telec16/pong/ltspice/ball_speed.asc

C1: cap; 100n
C3: cap; 10µ
C4: cap; 470n
D1: diode; 1N4148
J1: njf; J111
Q1: npn; BC547B
Q2: npn; BC547B
Q3: pnp; BC557B
R1: res; 10k
R2: res; 10k
R3: res; 100k
R4: res; 330k
R5: res; 1k
R6: res; 100k
R7: res; 10k
R8: res; 10k
U1: opamp2; TL082
U2: opamp2; TL082
U3: opamp2; TL082
V1: voltage; 15
V2: voltage; 15
V3: voltage; PULSE(0 5 0 0 0 100m 5)
V4: voltage; PULSE(0 5 0 0 0 1000m 25)
V5: voltage; PULSE(5 0 0 0 0 1000m 25)
Named nets: 0, +15, -15, speed, reset, _speed, pos, inc, reset_speed
.tran 50 startup
* TL082 OPERATIONAL AMPLIFIER "MACROMODEL" SUBCIRCUIT
* CREATED USING PARTS RELEASE 4.01 ON 06/16/89 AT 13:08
* (REV N/A)      SUPPLY VOLTAGE: +/-15V
* CONNECTIONS:   NON-INVERTING INPUT
*                | INVERTING INPUT
*                | | POSITIVE POWER SUPPLY
*                | | | NEGATIVE POWER SUPPLY
*                | | | | OUTPUT
*                | | | | |
.SUBCKT TL082    1 2 3 4 5
*
  C1   11 12 3.498E-12
  C2    6  7 15.00E-12
  DC    5 53 DX
  DE   54  5 DX
  DLP  90 91 DX
  DLN  92 90 DX
  DP    4  3 DX
  EGND 99  0 POLY(2) (3,0) (4,0) 0 .5 .5
  FB    7 99 POLY(5) VB VC VE VLP VLN 0 4.715E6 -5E6 5E6 5E6 -5E6
  GA    6  0 11 12 282.8E-6
  GCM   0  6 10 99 8.942E-9
  ISS   3 10 DC 195.0E-6
  HLIM 90  0 VLIM 1K
  J1   11  2 10 JX
  J2   12  1 10 JX
  R2    6  9 100.0E3
  RD1   4 11 3.536E3
  RD2   4 12 3.536E3
  RO1   8  5 150
  RO2   7 99 150
  RP    3  4 2.143E3
  RSS  10 99 1.026E6
  VB    9  0 DC 0
  VC    3 53 DC 2.200
  VE   54  4 DC 2.200
  VLIM  7  8 DC 0
  VLP  91  0 DC 25
  VLN   0 92 DC 25
.MODEL DX D(IS=800.0E-18)
.MODEL JX PJF(IS=15.00E-12 BETA=270.1E-6 VTO=-1)
.ENDS
