telec16/pong/ltspice/and_or.asc

D1: diode; 1N4148
D2: diode; 1N4148
D3: diode; 1N4148
D4: diode; 1N4148
D5: diode; 1N4148
D6: diode; 1N4148
Q1: npn; BC547B
Q2: npn; BC547B
R1: res; 10k
R2: res; 10k
R3: res; 10k
R4: res; 10k
R5: res; 100k
V1: voltage; PULSE(0 5 0 0 0 8 16)
V2: voltage; PULSE(0 5 0 0 0 4 8)
V3: voltage; PULSE(0 5 0 0 0 2 4)
V4: voltage; PULSE(0 5 0 0 0 1 2)
V5: voltage; 5
Named nets: 0, D, A, 5V, out, _out, B, C
