telec16/pong/ltspice/pad_area.asc

D1: diode; 1N4148
D2: diode; 1N4148
Q1: npn; BC547B
Q2: npn; BC547B
Q3: npn; BC547B
Q4: npn; BC547B
R1: res; 10k
R2: res; 10k
R3: res; 4k7
R4: res; 10k
R5: res; 10k
R6: res; 4k7
R7: res; 10k
R8: res; 10k
R9: res; 100
R10: res; 1k
R11: res; 10k
R12: res; 10k
R13: res; 10k
R14: res; 10k
U1: opamp2; LM393A
U2: opamp2; LM393A
U3: opamp2; LM393A
V1: voltage; 15
V2: voltage; 15
V3: voltage; 5
V4: voltage; PULSE(-5 5 0 1 0 0 1)
V5: voltage; 2
V6: voltage; PULSE(4.8 4.2 0 0 0 1 2)
Named nets: 0, +15, -15, +5, pad, bally, edge, pad+, pad-, ballx
.tran 2 startup
* LM393A VOLTAGE COMPARATOR "MACROMODEL" SUBCIRCUIT
* CREATED USING PARTS VERSION 4.03 ON 03/07/90 AT 14:17
* REV (N/A)
* CONNECTIONS:   NON-INVERTING INPUT
*                | INVERTING INPUT
*                | | POSITIVE POWER SUPPLY
*                | | | NEGATIVE POWER SUPPLY
*                | | | | OPEN COLLECTOR OUTPUT
*                | | | | |
.SUBCKT LM393A   1 2 3 4 5
*
  F1    9  3 V1 1
  IEE   3  7 DC 100.0E-6
  VI1  21  1 DC .75
  VI2  22  2 DC .75
  Q1    9 21  7 QIN
  Q2    8 22  7 QIN
  Q3    9  8  4 QMO
  Q4    8  8  4 QMI
.MODEL QIN PNP(IS=800.0E-18 BF=2.000E3)
.MODEL QMI NPN(IS=800.0E-18 BF=1002)
.MODEL QMO NPN(IS=800.0E-18 BF=1000 CJC=1E-15 TR=807.4E-9)
  E1   10  4  9  4  1
  V1   10 11 DC 0
  Q5    5 11  4 QOC
.MODEL QOC NPN(IS=800.0E-18 BF=20.29E3 CJC=1E-15 TF=942.6E-12 TR=543.8E-9)
  DP    4  3 DX
  RP 3  4 46.3E3
.MODEL DX  D(IS=800.0E-18)
*
.ENDS
